EngLuizs/Fonte_Linear_12V/Firmware/src/images.cpp

#include <Arduino.h>
#include "images.h"

// ======================================================================
//                         LOGO FLM SYSTEMS
// ======================================================================
  // array size is 7299
  const unsigned char FLM_Systems_Logo[] PROGMEM  = {
    0x89, 0x50, 0x4e, 0x47, 0x0d, 0x0a, 0x1a, 0x0a, 0x00, 0x00, 0x00, 0x0d, 0x49, 0x48, 0x44, 0x52, 
    0x00, 0x00, 0x00, 0xe4, 0x00, 0x00, 0x00, 0x35, 0x08, 0x06, 0x00, 0x00, 0x00, 0x51, 0x35, 0x47, 
    0x07, 0x00, 0x00, 0x00, 0x01, 0x73, 0x52, 0x47, 0x42, 0x00, 0xae, 0xce, 0x1c, 0xe9, 0x00, 0x00, 
    0x00, 0x04, 0x67, 0x41, 0x4d, 0x41, 0x00, 0x00, 0xb1, 0x8f, 0x0b, 0xfc, 0x61, 0x05, 0x00, 0x00, 
    0x00, 0x09, 0x70, 0x48, 0x59, 0x73, 0x00, 0x00, 0x0e, 0xc4, 0x00, 0x00, 0x0e, 0xc4, 0x01, 0x95, 
    0x2b, 0x0e, 0x1b, 0x00, 0x00, 0x1c, 0x18, 0x49, 0x44, 0x41, 0x54, 0x78, 0x5e, 0xed, 0x9c, 0x79, 
    0x94, 0x25, 0x55, 0x9d, 0xe7, 0xbf, 0xbf, 0x1b, 0xf1, 0xf6, 0x7c, 0x4b, 0x66, 0xbe, 0x97, 0x4b, 
    0x55, 0x66, 0x16, 0x0c, 0x50, 0x50, 0x58, 0x22, 0x4b, 0x81, 0x28, 0x0a, 0x05, 0x82, 0xd8, 0x8d, 
    0x80, 0x7d, 0x1c, 0xd0, 0x06, 0x4e, 0x8f, 0x72, 0x86, 0xd6, 0x69, 0x9b, 0x6e, 0x84, 0x91, 0xc1, 
    0x1e, 0xec, 0x1c, 0x46, 0x0f, 0x33, 0xb6, 0x88, 0x76, 0xe3, 0x20, 0x8b, 0x8e, 0xa2, 0xb6, 0xed, 
    0x64, 0xa1, 0xb8, 0xf4, 0x74, 0x0f, 0xb2, 0x54, 0x41, 0x63, 0x8b, 0x35, 0x80, 0x0a, 0xc5, 0x62, 
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
    0xe8, 0xec, 0xdf, 0x64, 0x67, 0x32, 0x7c, 0x7f, 0x00, 0x20, 0x8f, 0x05, 0x63, 0x51, 0xbb, 0x64, 
    0x69, 0xe3, 0xff, 0x2d, 0x2f, 0x3e, 0xef, 0xad, 0x7b, 0x36, 0x5b, 0x29, 0xd3, 0xfd, 0x78, 0x09, 
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
  };
  const unsigned int Fonte_de_Bancada_len = 11789;
