EngLuizs/Fonte_Linear_12V/Firmware/src/images.h

#pragma once

extern const unsigned char FLM_Systems_Logo[];
extern const unsigned int FLM_Systems_Logo_len;

extern const unsigned char Fonte_de_Bancada[];
extern const unsigned int Fonte_de_Bancada_len;
